Safecast/Solarcast/air-module/Bottom.png

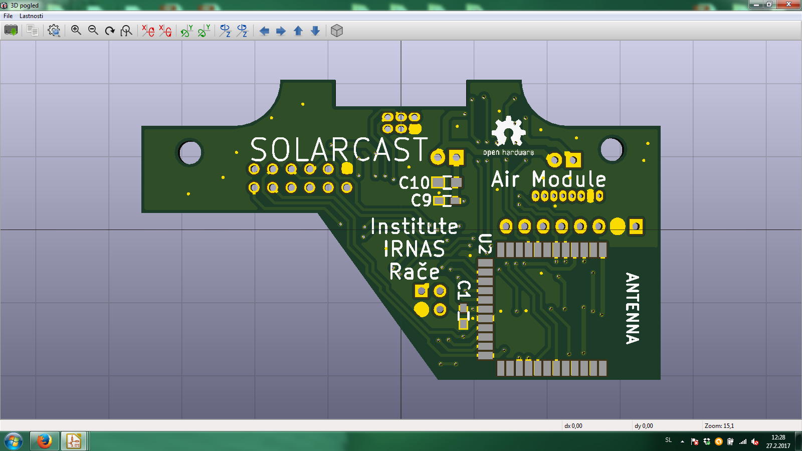
air-module/Bottom.png
