Safecast/Solarcast/air-module/Top.png

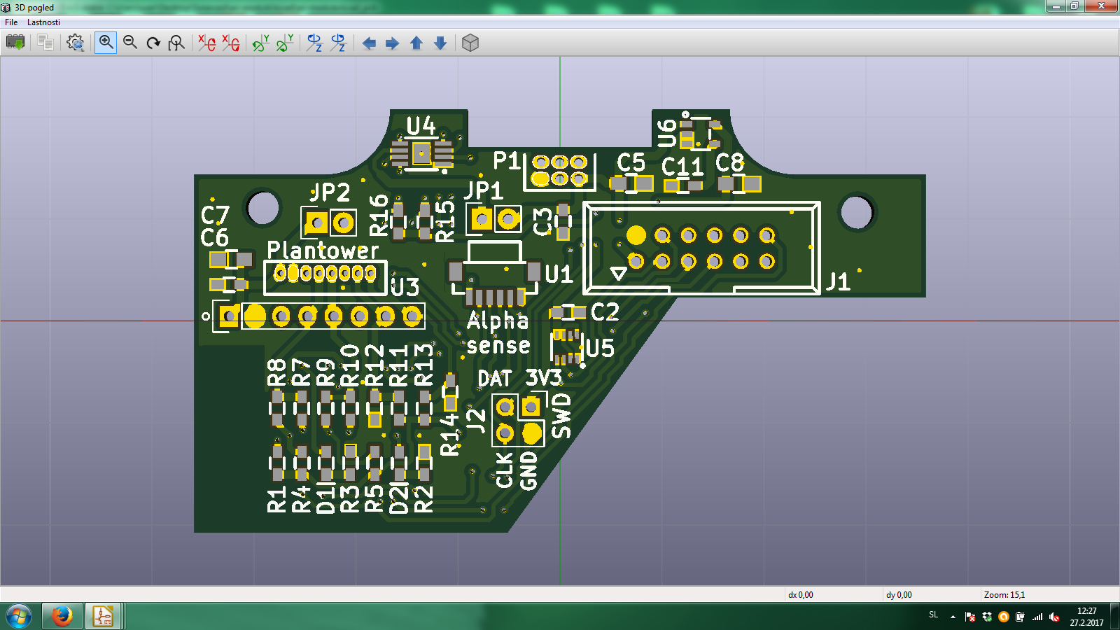
air-module/Top.png
