Safecast/Solarcast/communications-module/bottom.png

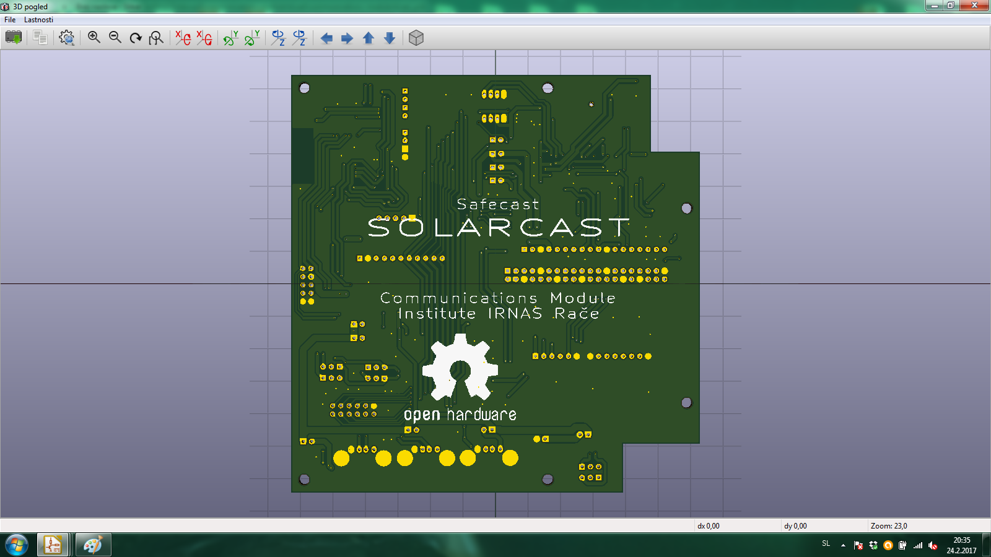
communications-module/bottom.png
