Safecast/Solarcast/communications-module/top.png

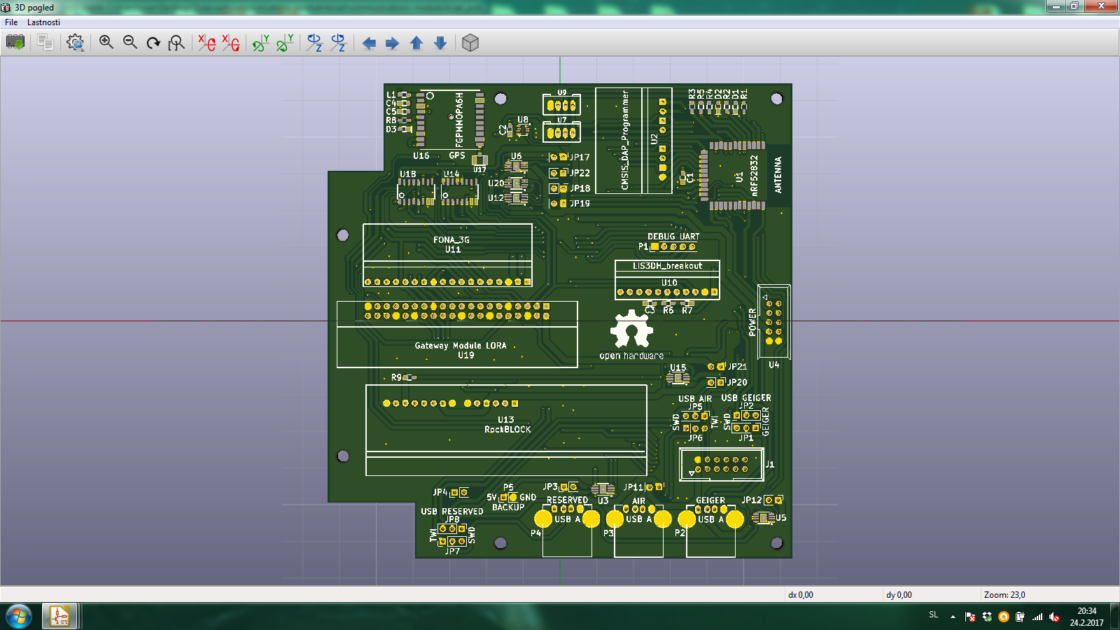
communications-module/top.png
