Safecast/Solarcast/gateway-module/bottom.png

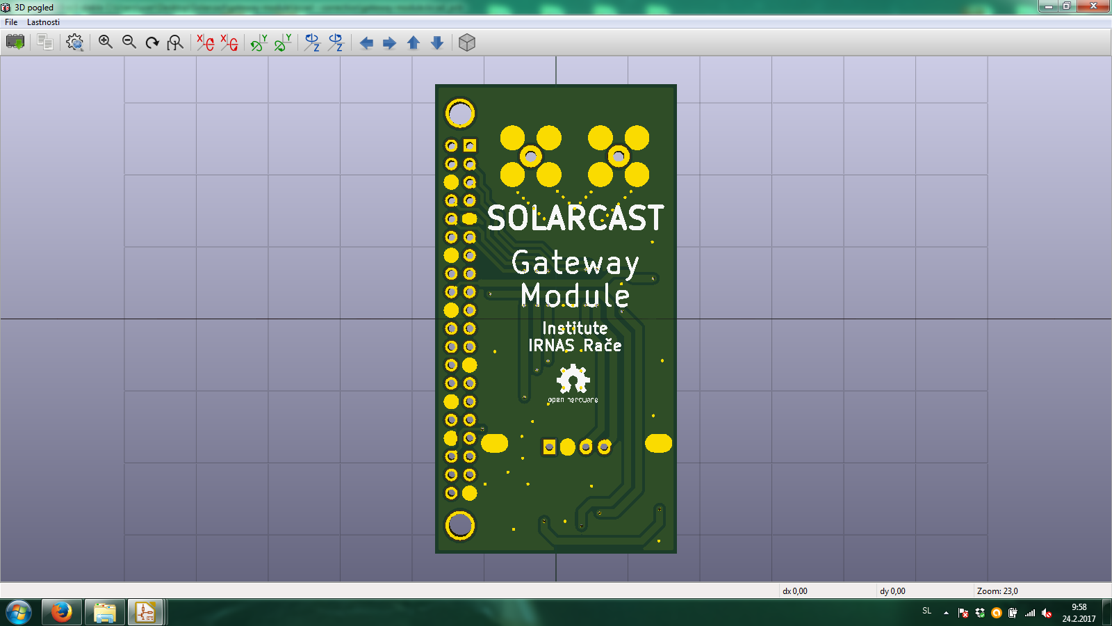
gateway-module/bottom.png
