Safecast/Solarcast/gateway-module/top.png

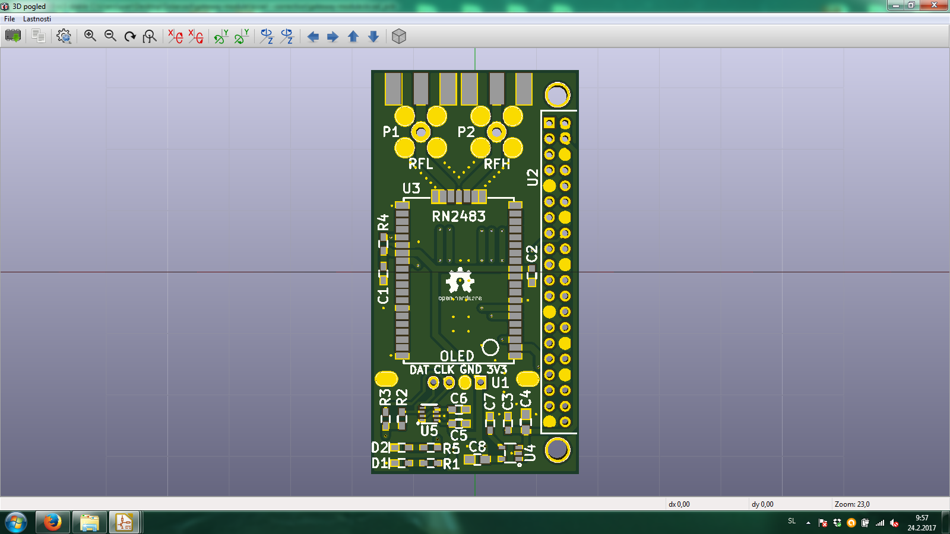
gateway-module/top.png
