Safecast/Solarcast/geiger-module/bottom.png

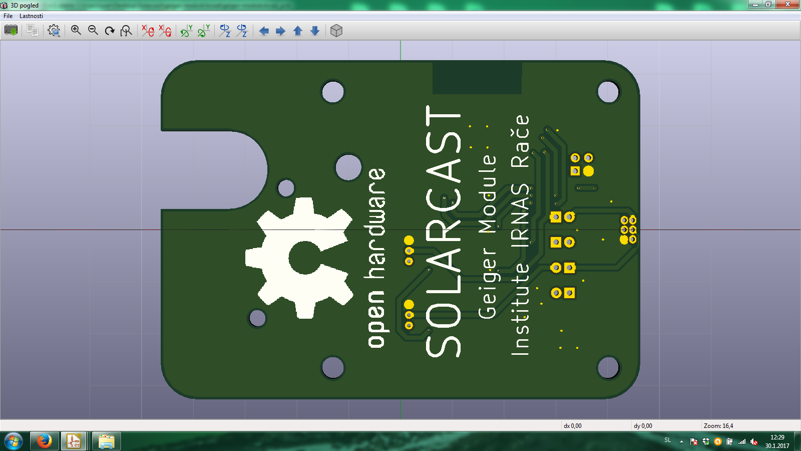
geiger-module/bottom.png
