Safecast/Solarcast/geiger-module/top.png

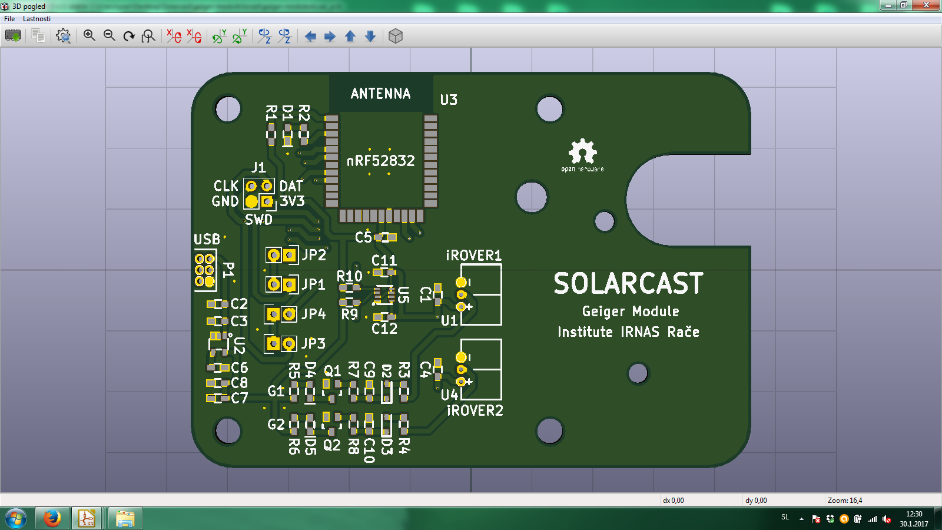
geiger-module/top.png
