Safecast/Solarcast/plantower-adapter/bottom.png

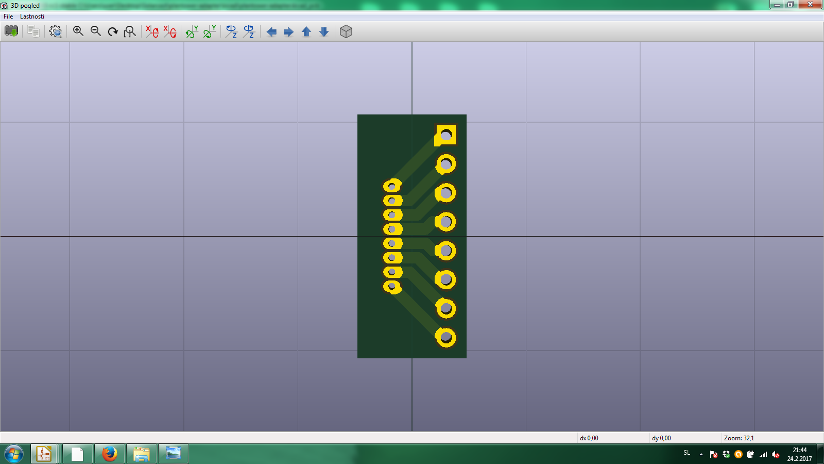
plantower-adapter/bottom.png
