Safecast/Solarcast/air-module/gerbers/air-module-B_Mask.pdf

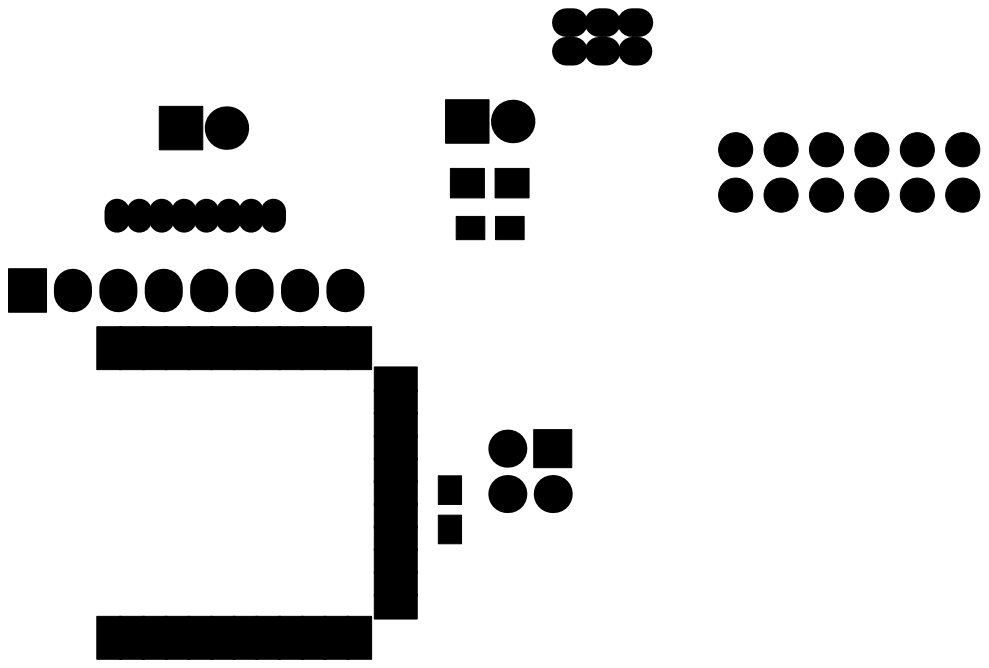
[picture p123: page 1]
