Safecast/Solarcast/air-module/gerbers/air-module-B_SilkS.pdf

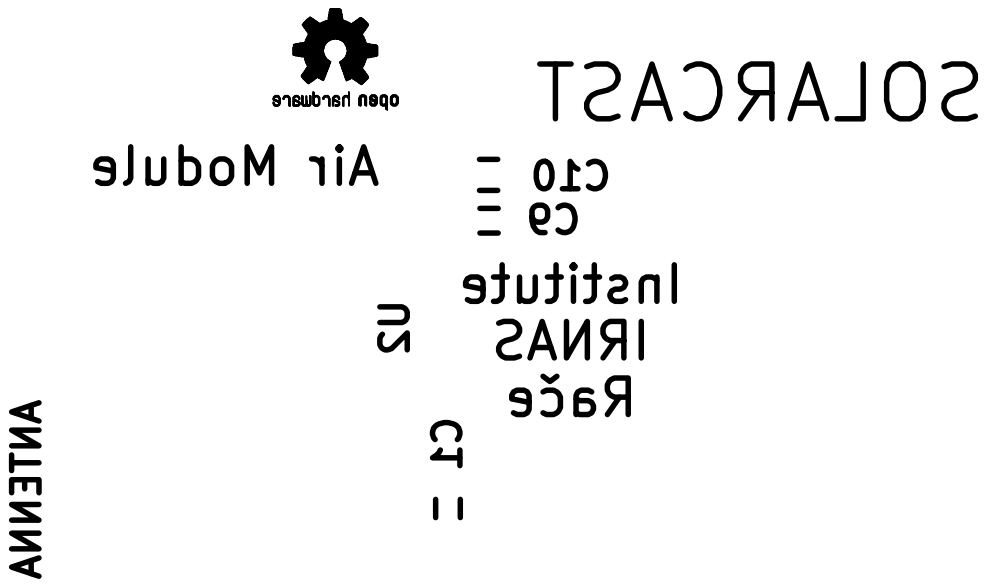
[picture p124: page 1]
