Safecast/Solarcast/air-module/gerbers/air-module-Edge_Cuts.pdf

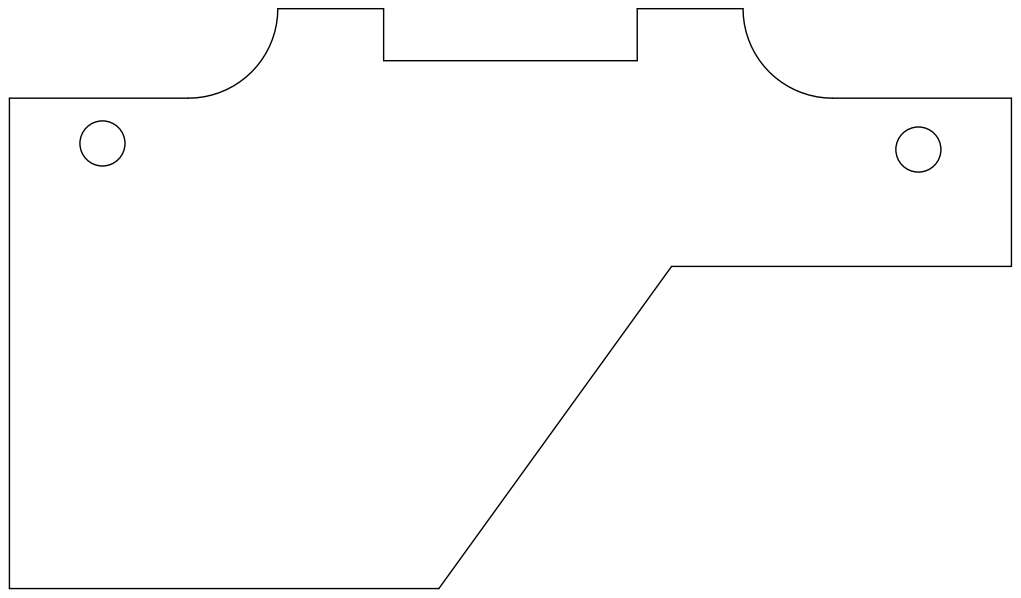
[picture p125: page 1]
