Safecast/Solarcast/air-module/gerbers/air-module-F_Cu.pdf

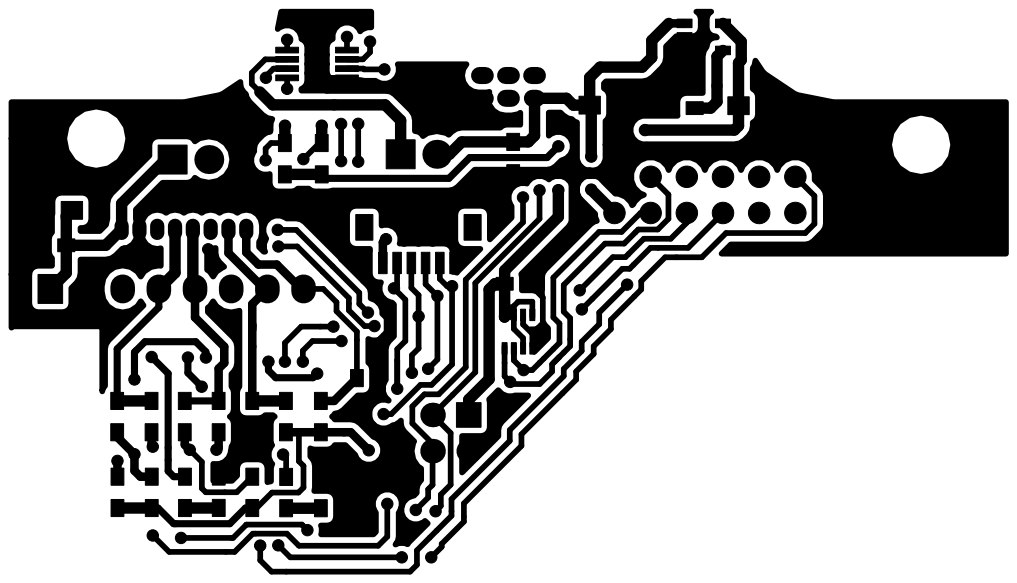
[picture p126: page 1]
