Safecast/Solarcast/air-module/gerbers/air-module-F_Mask.pdf

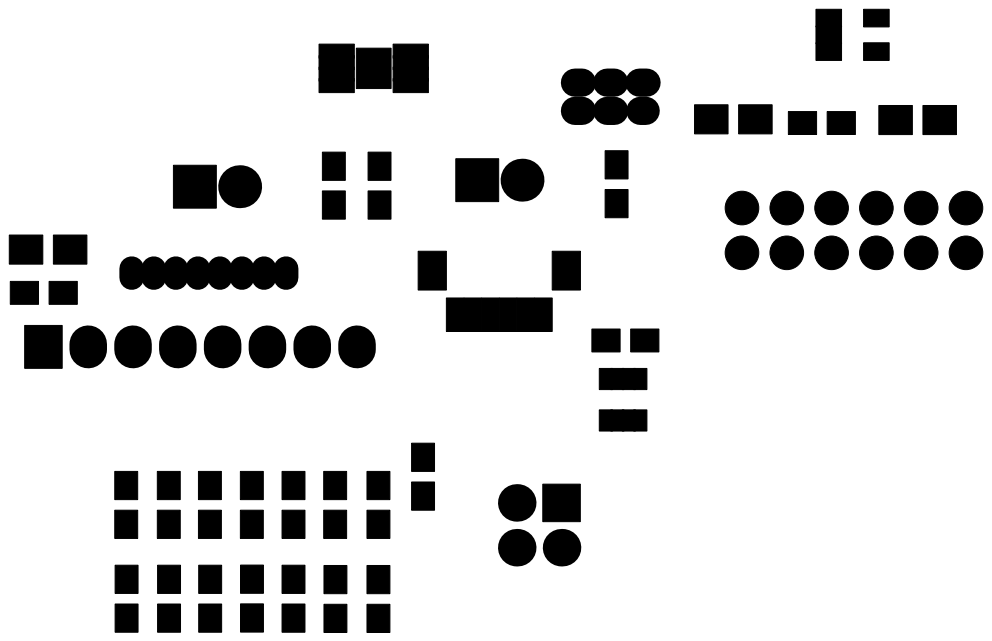
[picture p127: page 1]
