Safecast/Solarcast/air-module/gerbers/air-module-F_SilkS.pdf

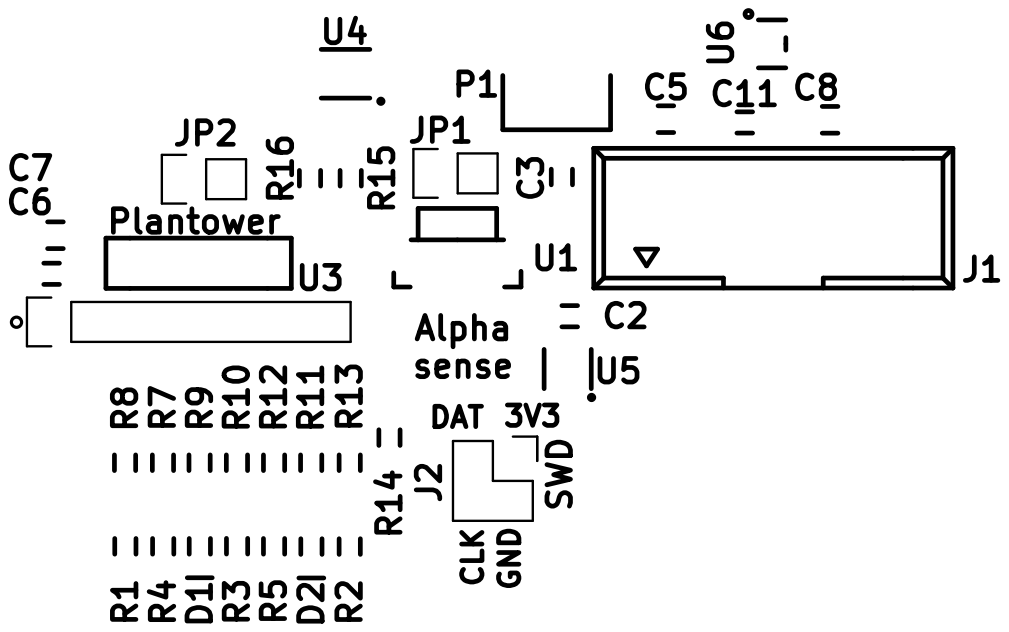
[picture p128: page 1]
