Safecast/Solarcast/plantower-adapter/gerbers/plantower-adapter-B_Cu.pdf

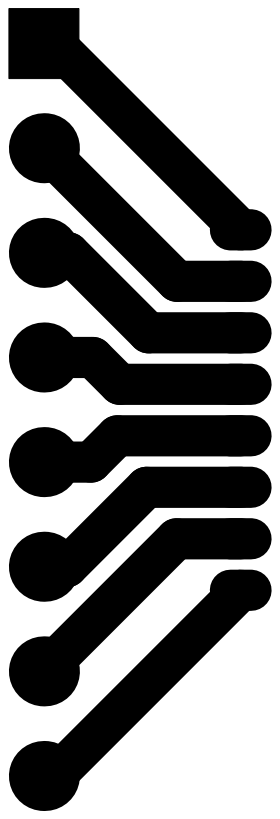
[picture p129: page 1]
