Safecast/Solarcast/communications-module/gerbers/communications-module-B_Cu.pdf

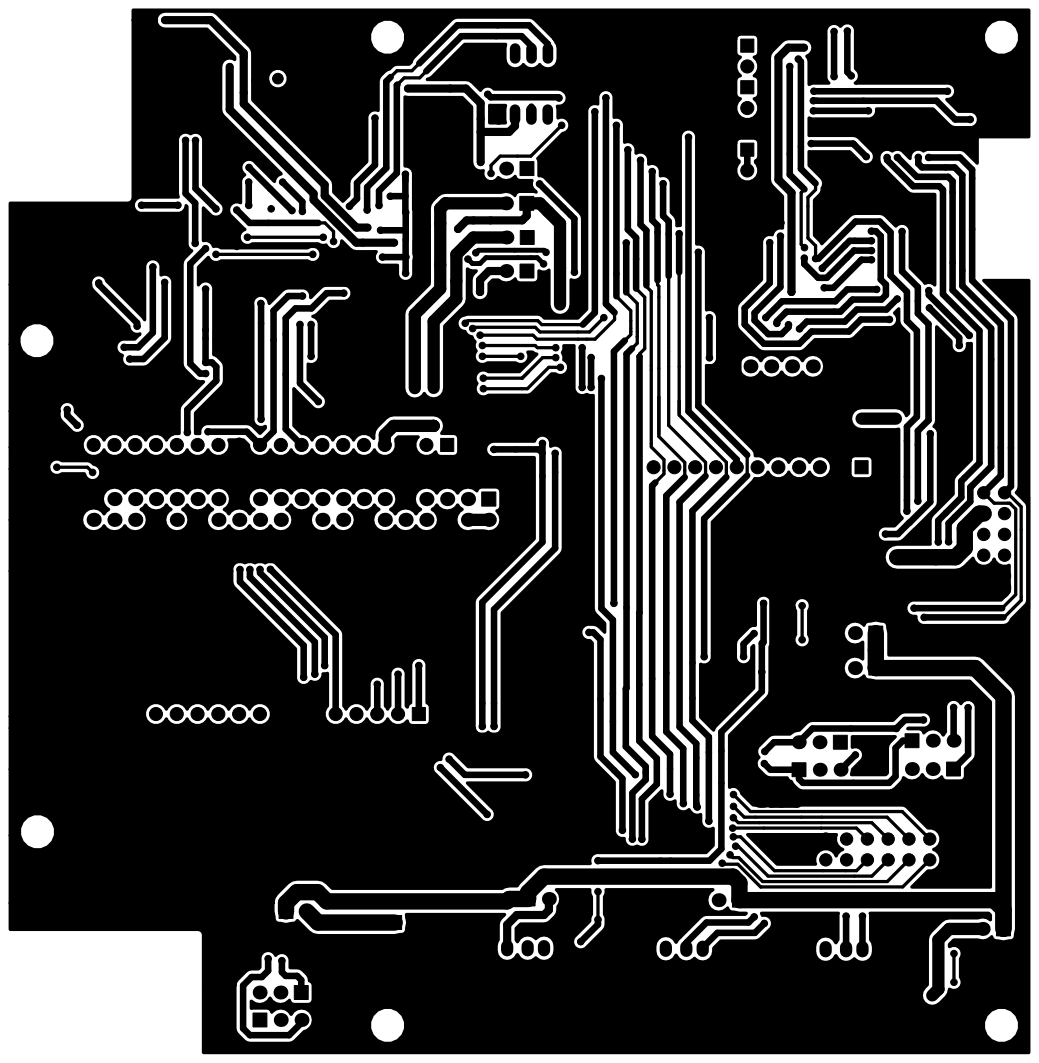
[picture p130: page 1]
