Safecast/Solarcast/communications-module/gerbers/communications-module-B_Mask.pdf

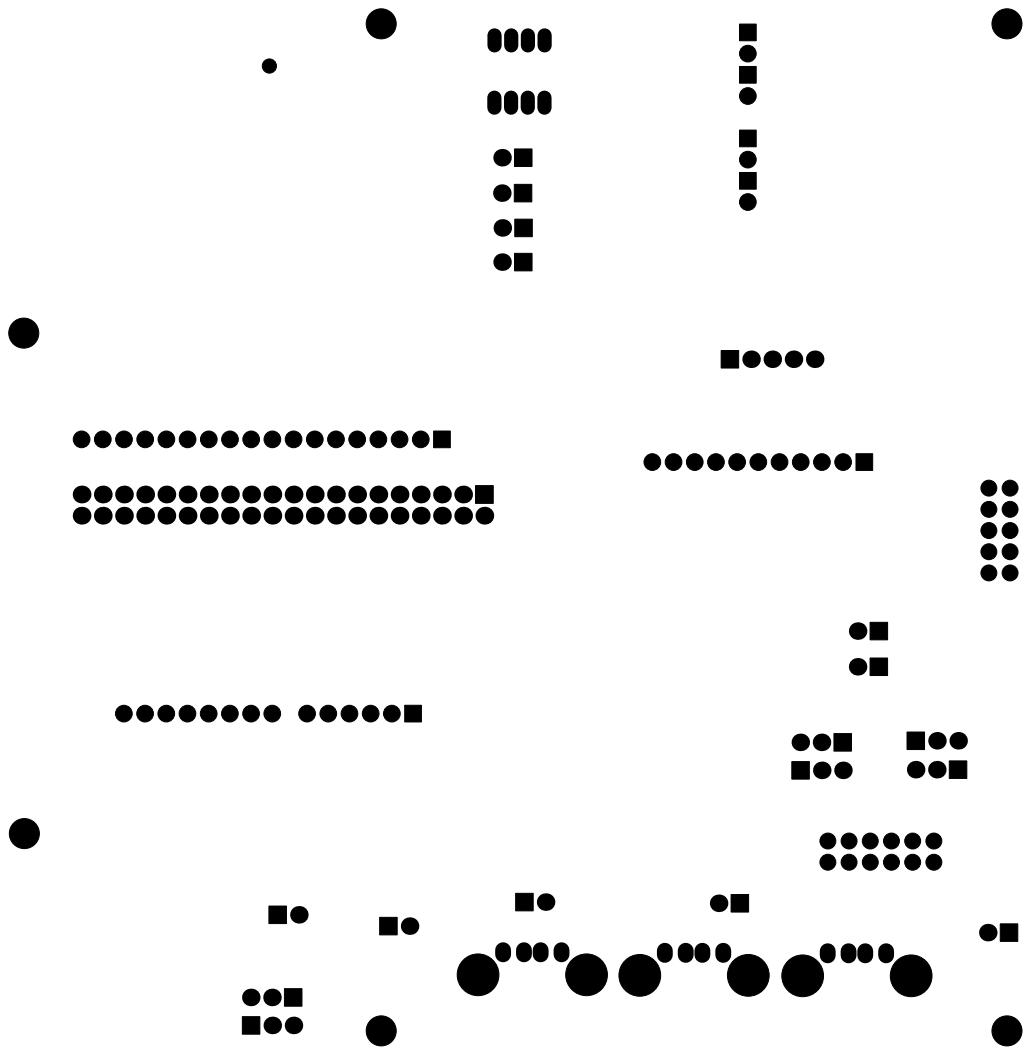
[picture p131: page 1]
