Safecast/Solarcast/communications-module/gerbers/communications-module-B_SilkS.pdf

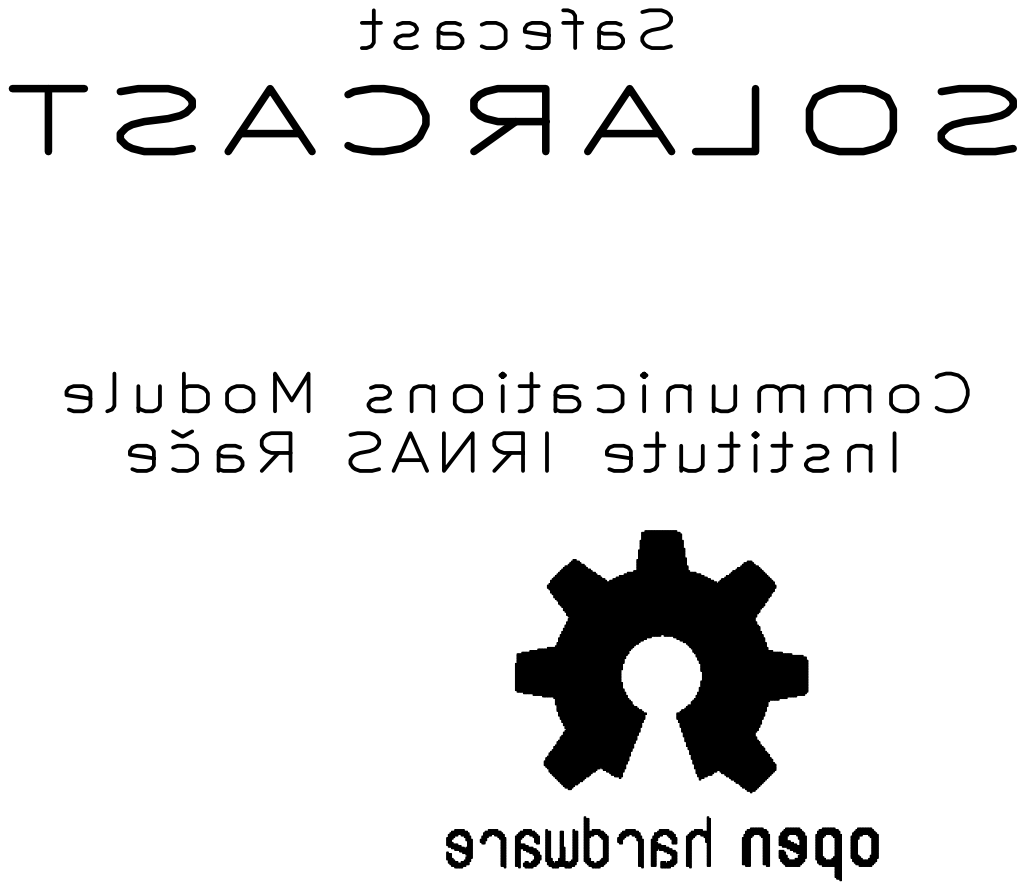
[picture p132: page 1]
