Safecast/Solarcast/communications-module/gerbers/communications-module-F_Cu.pdf

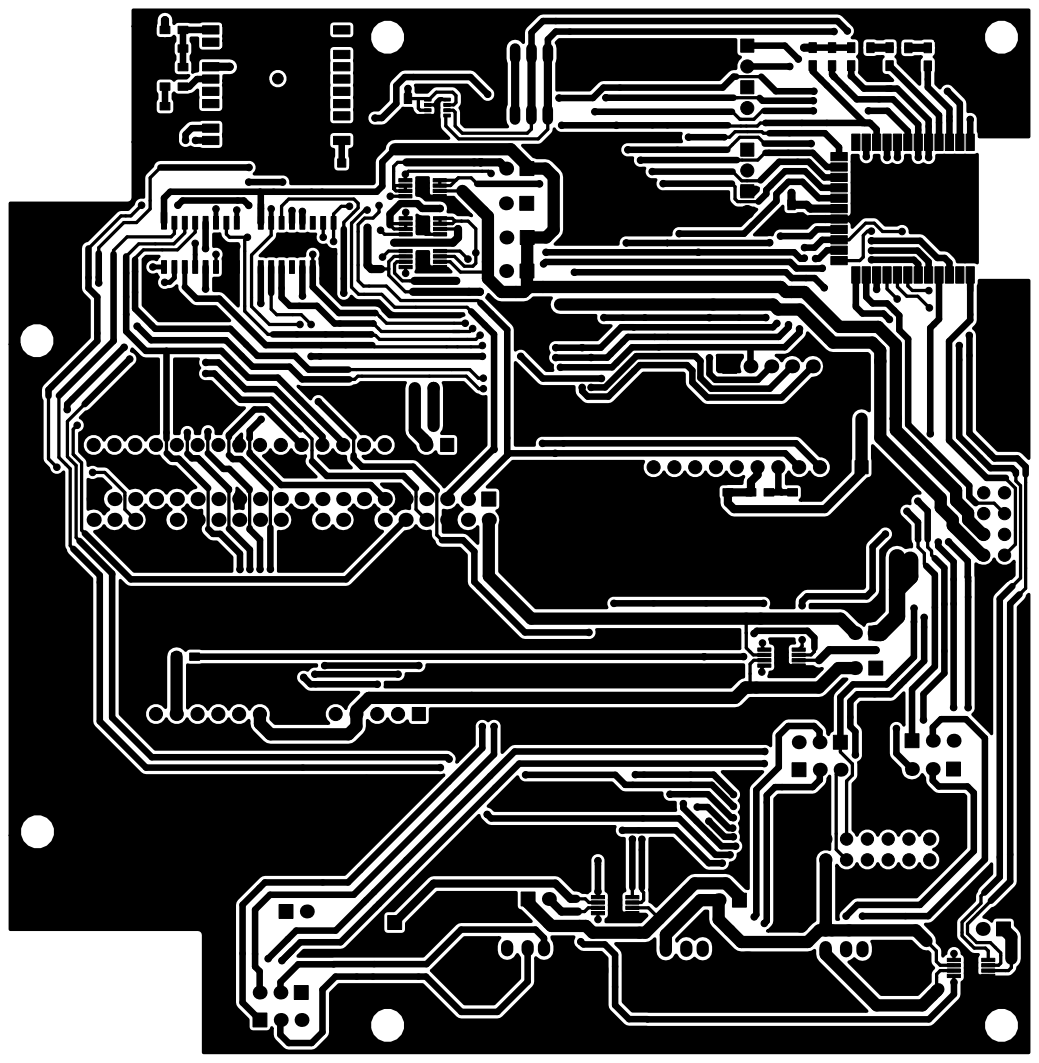
[picture p133: page 1]
