Safecast/Solarcast/communications-module/gerbers/communications-module-F_Mask.pdf

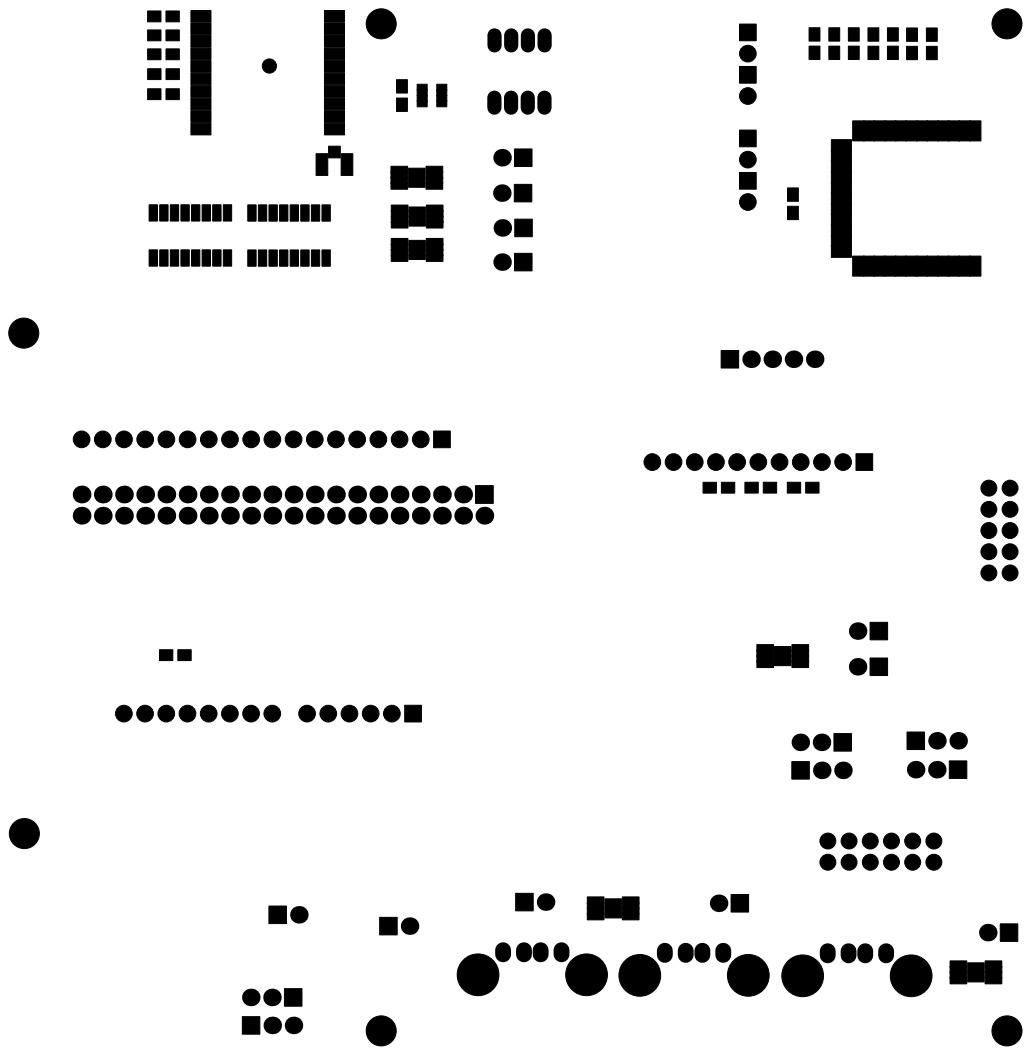
[picture p134: page 1]
