Safecast/Solarcast/communications-module/gerbers/communications-module-F_SilkS.pdf

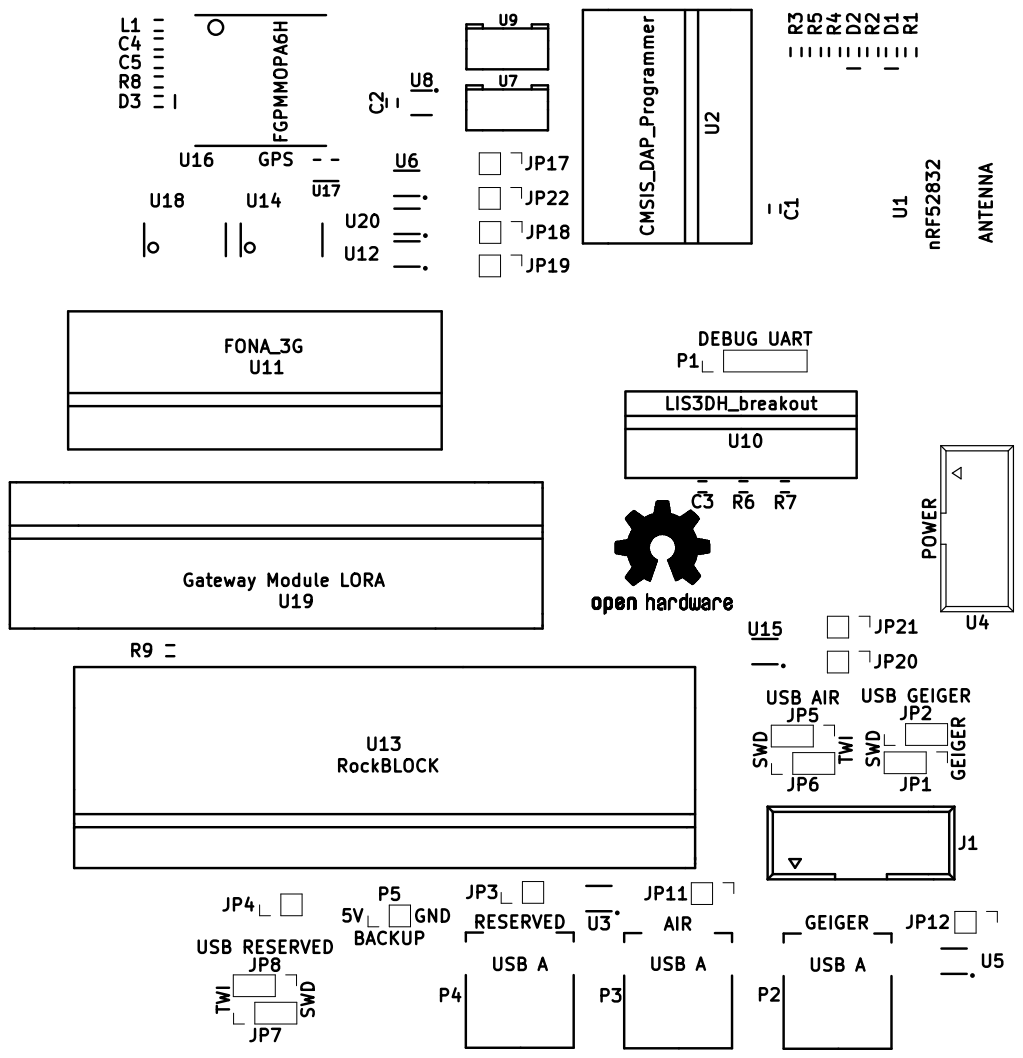
[picture p135: page 1]
