Safecast/Solarcast/gateway-module/gerbers/gateway-module-B_Cu.pdf

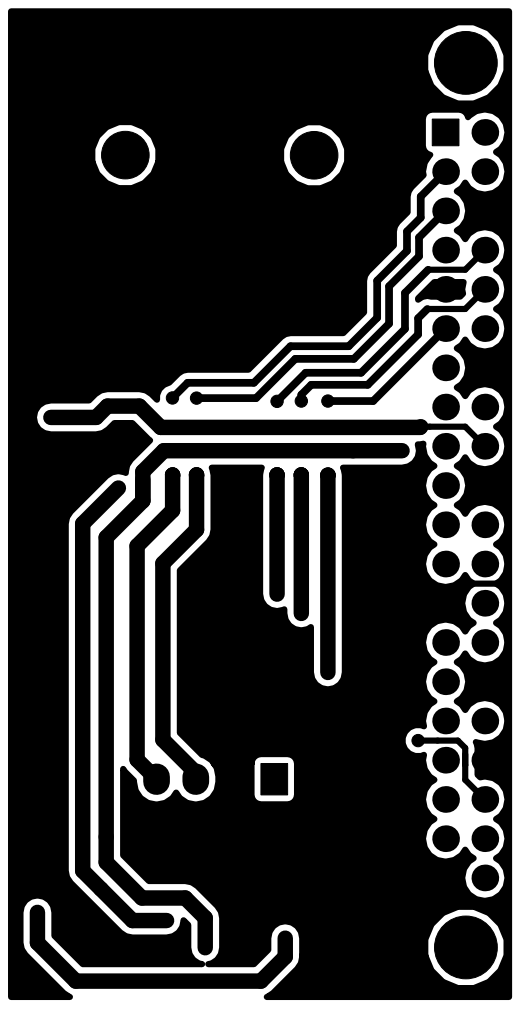
[picture p136: page 1]
