Safecast/Solarcast/gateway-module/gerbers/gateway-module-B_Mask.pdf

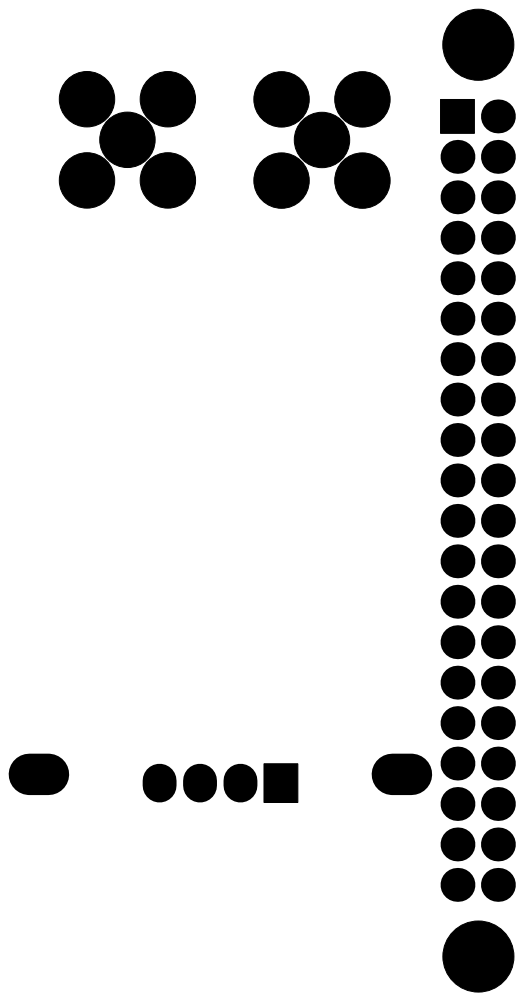
[picture p137: page 1]
