Safecast/Solarcast/gateway-module/gerbers/gateway-module-B_SilkS.pdf

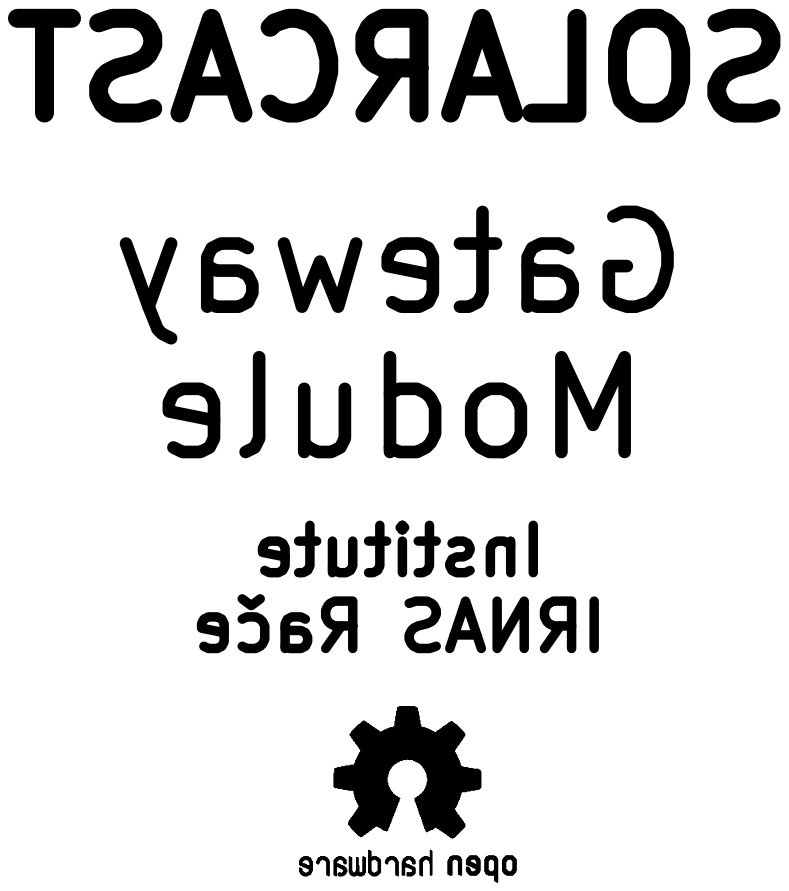
[picture p138: page 1]
