Safecast/Solarcast/gateway-module/gerbers/gateway-module-F_Cu.pdf

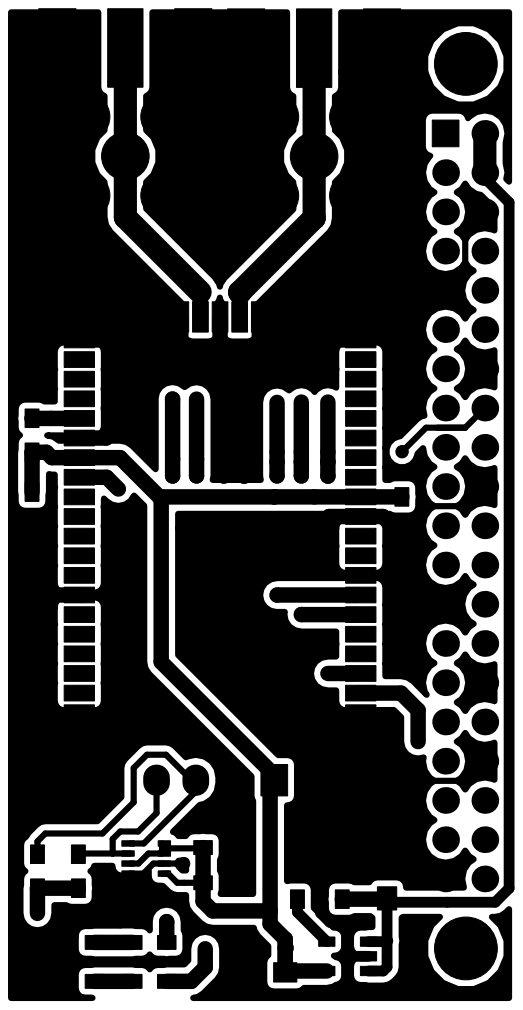
[picture p139: page 1]
