Safecast/Solarcast/gateway-module/gerbers/gateway-module-F_Mask.pdf

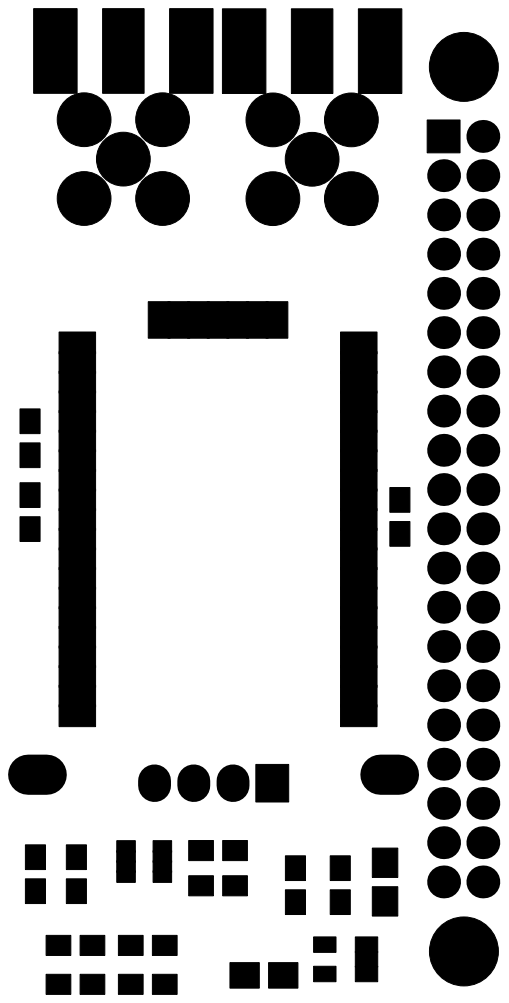
[picture p140: page 1]
