Safecast/Solarcast/gateway-module/gerbers/gateway-module-F_SilkS.pdf

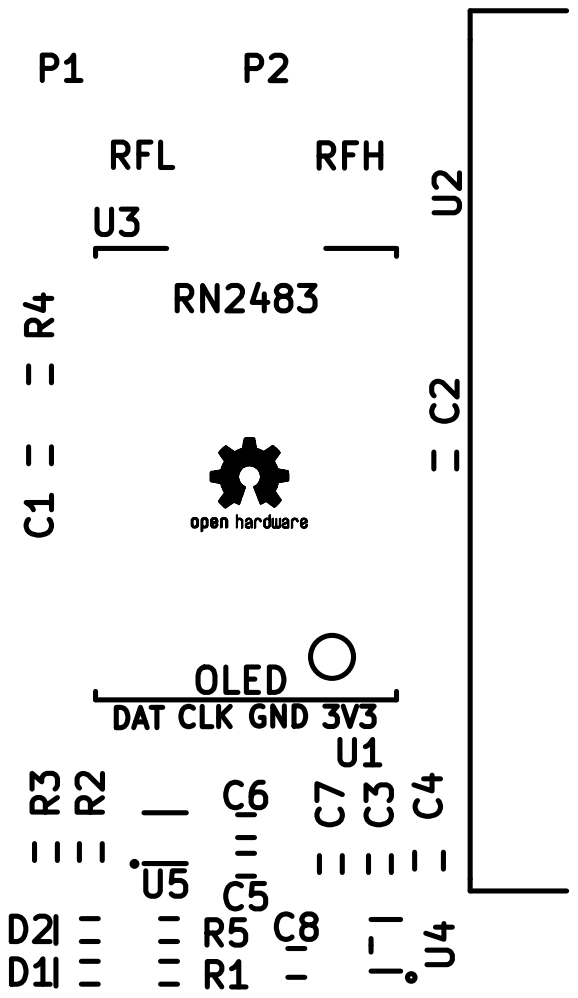
[picture p141: page 1]
