Safecast/Solarcast/gateway-module/kicad/gateway-module.pdf

File: gateway-module.sch Sheet: /
Id: 1/1 Title: Communications Module
