Safecast/Solarcast/geiger-module/gerbers/geiger-module-B_Cu.pdf

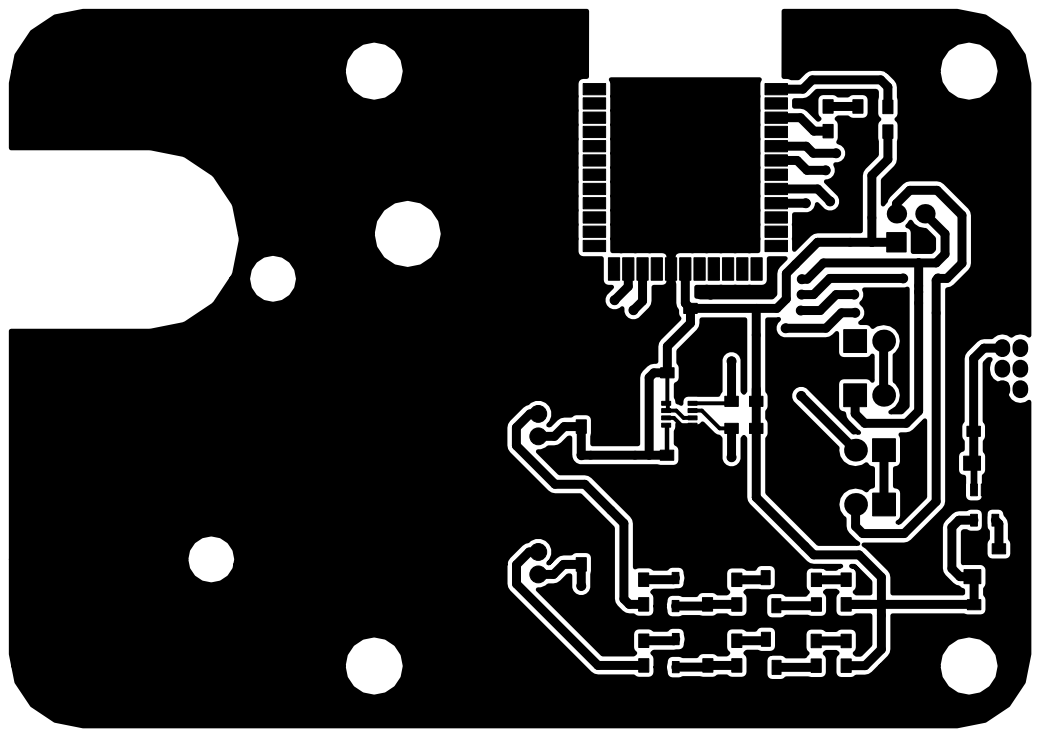
[picture p142: page 1]
