Safecast/Solarcast/geiger-module/gerbers/geiger-module-B_Mask.pdf

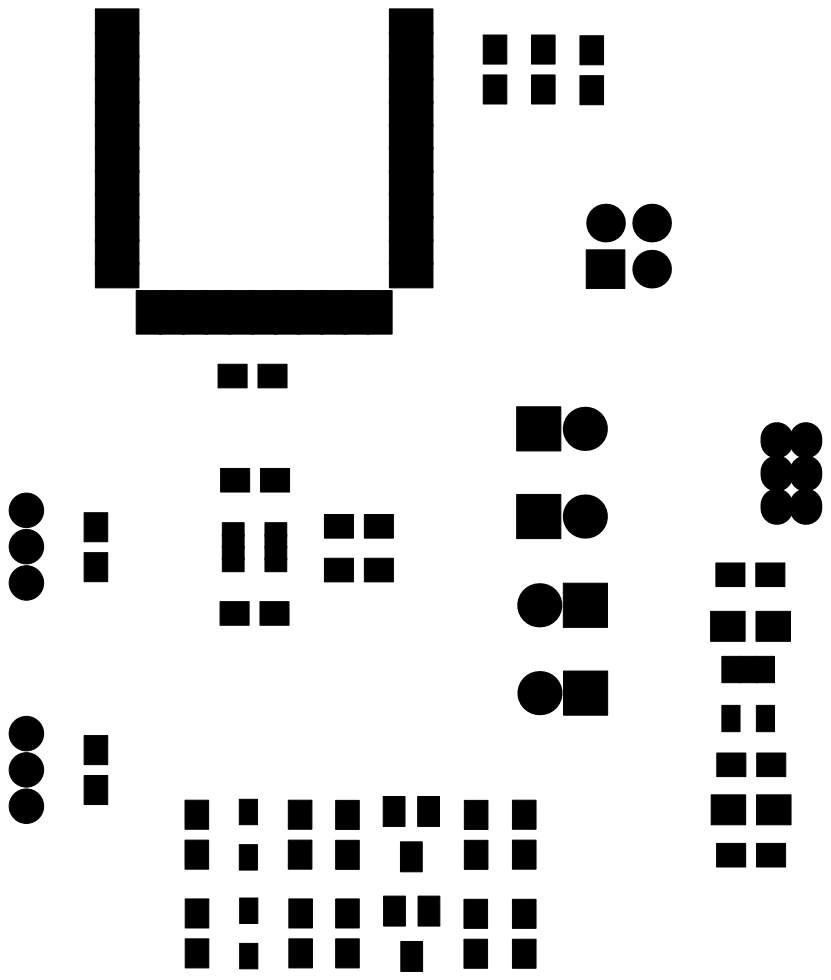
[picture p143: page 1]
