Safecast/Solarcast/geiger-module/gerbers/geiger-module-B_SilkS.pdf

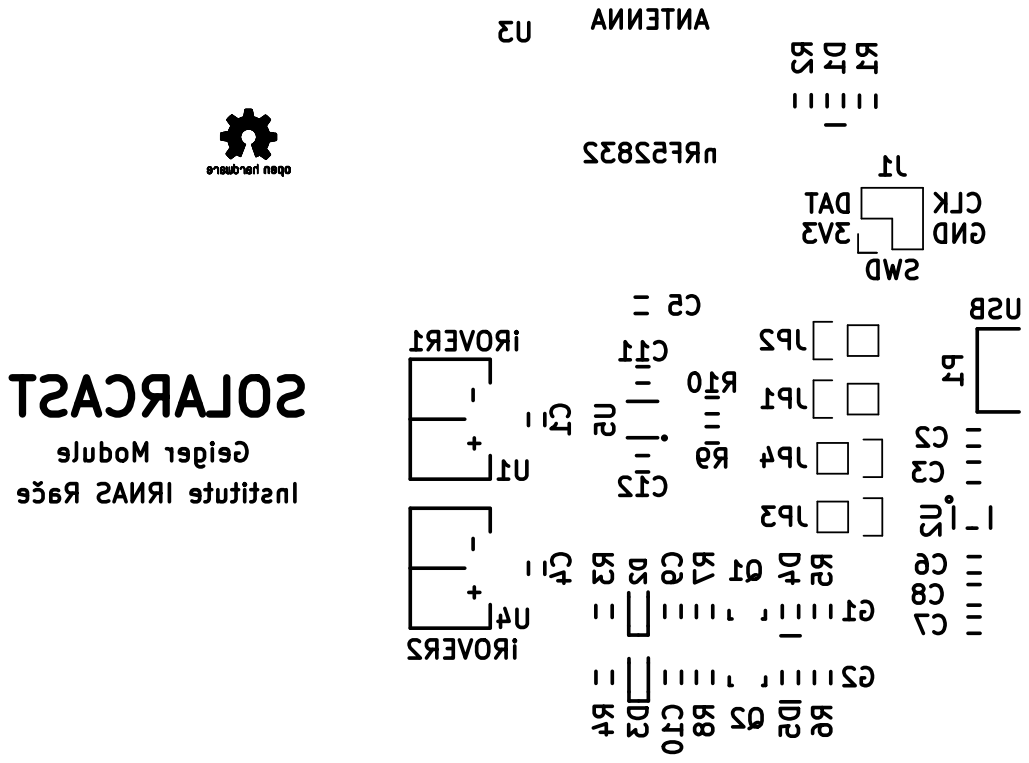
[picture p144: page 1]

Institute IRNAS Rae Geiger Module
