Safecast/Solarcast/geiger-module/gerbers/geiger-module-Edge_Cuts.pdf

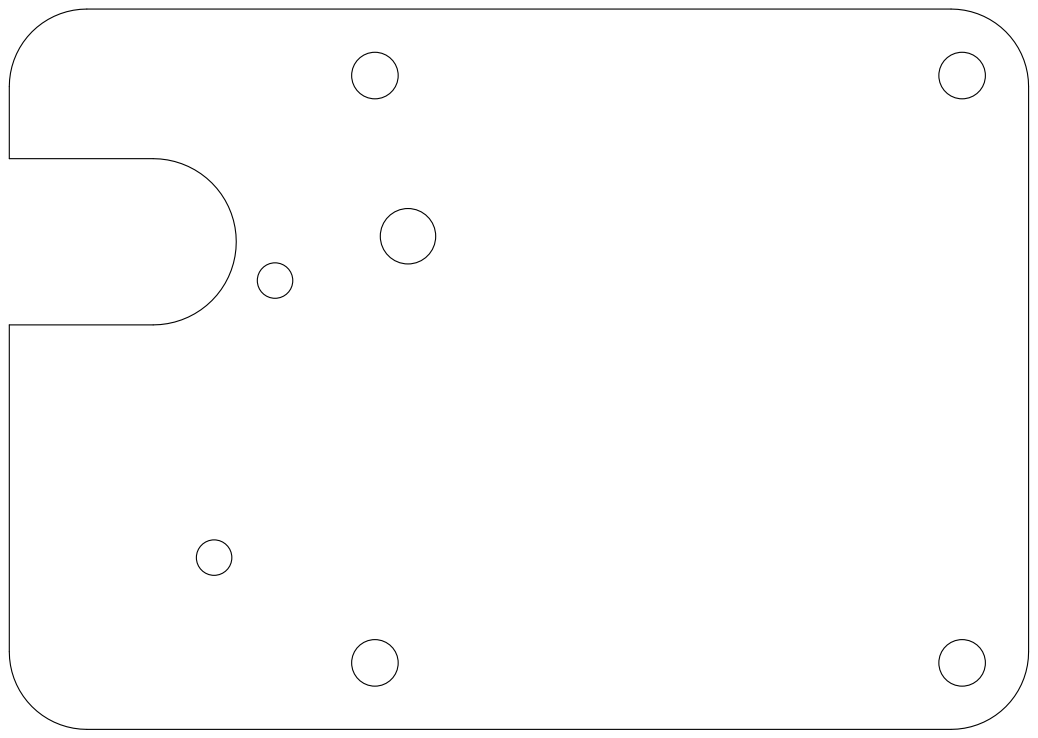
[picture p145: page 1]
