Safecast/Solarcast/geiger-module/gerbers/geiger-module-F_Cu.pdf

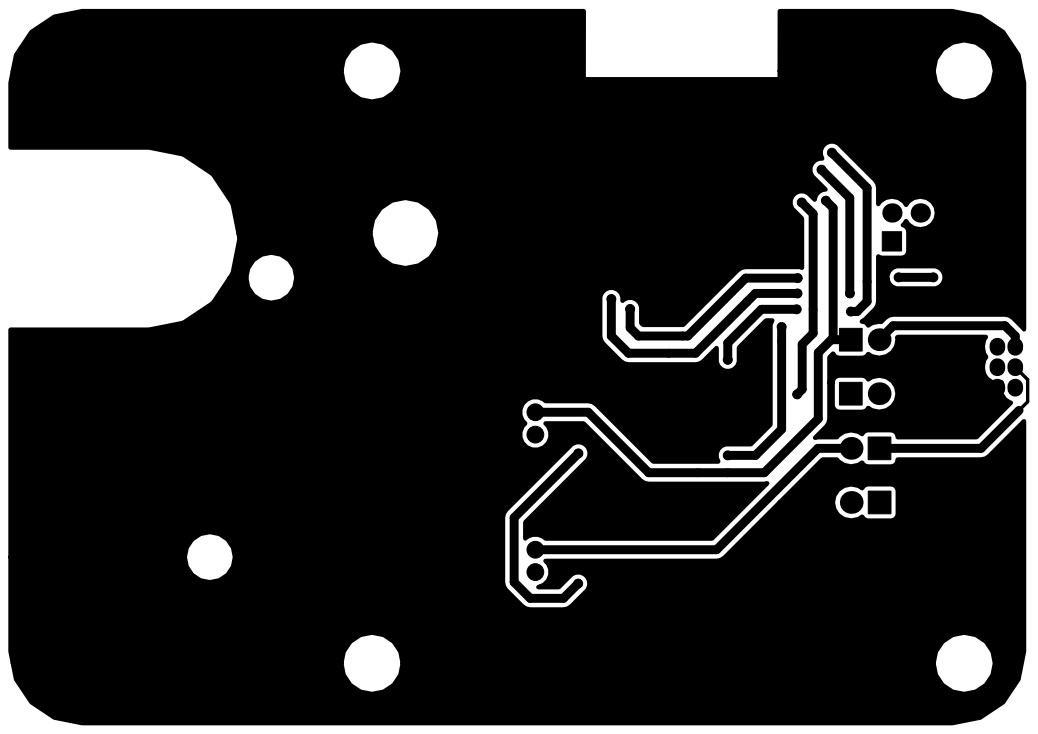
[picture p146: page 1]
