Safecast/Solarcast/geiger-module/gerbers/geiger-module-F_Mask.pdf

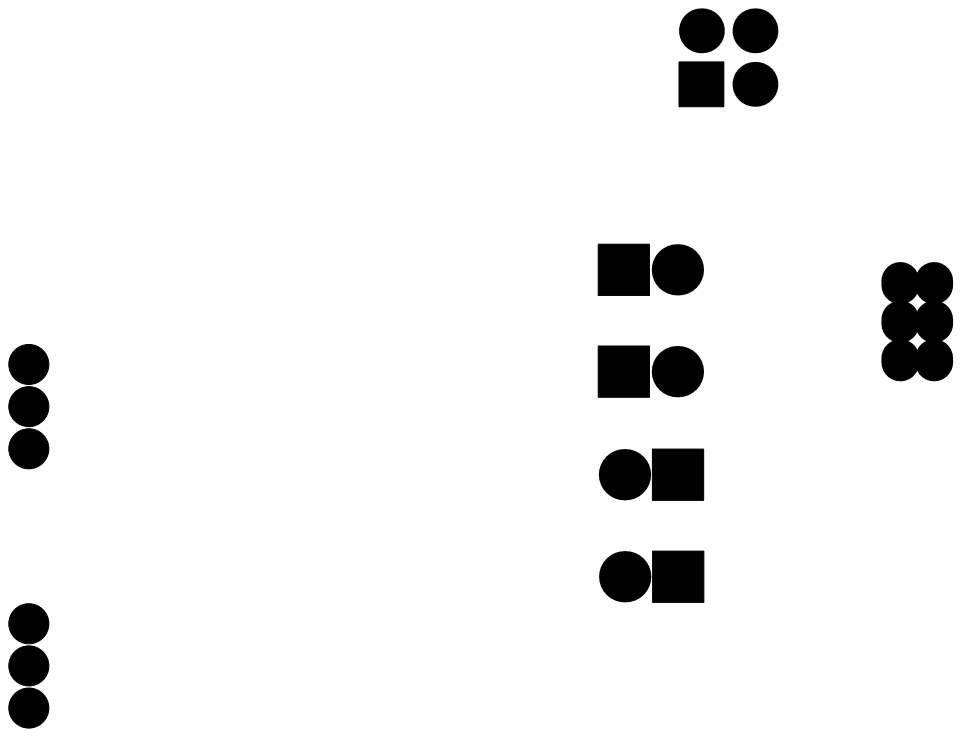
[picture p147: page 1]
