Safecast/Solarcast/geiger-module/gerbers/geiger-module-F_SilkS.pdf

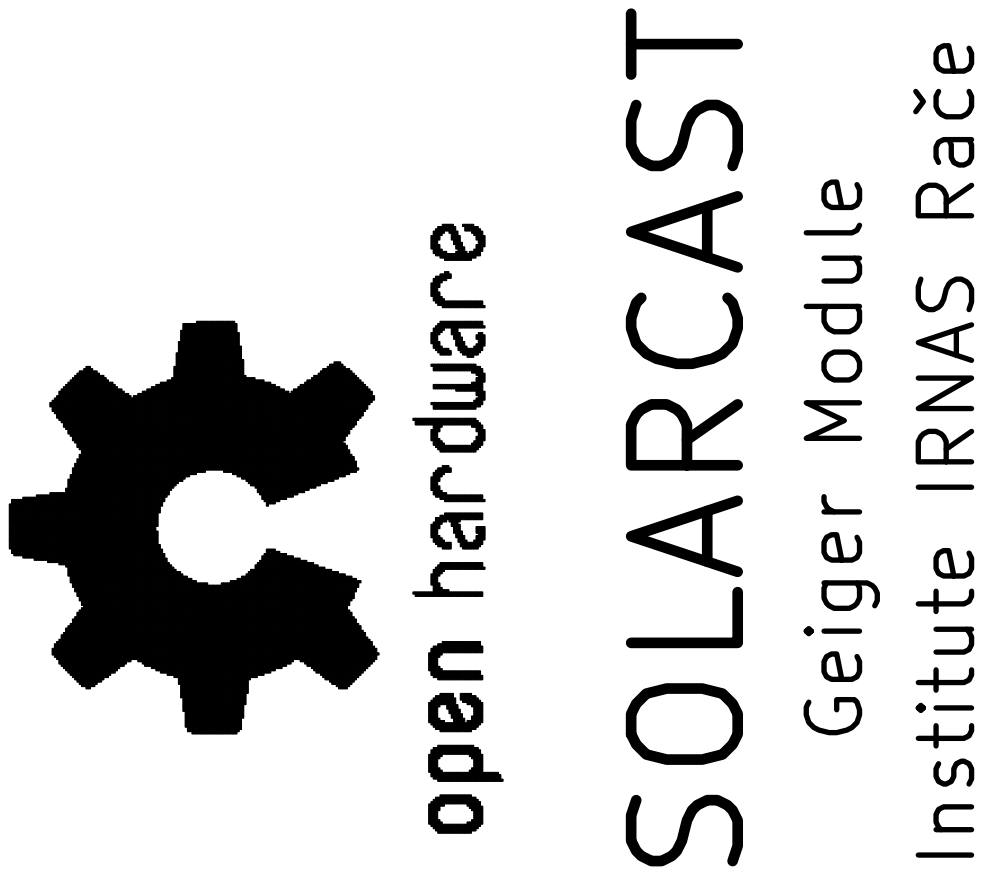
[picture p148: page 1]

Institute IRNAS Rae Geiger Module SOLARCAST
