Safecast/Solarcast/geiger-module/kicad/geiger-module.pdf

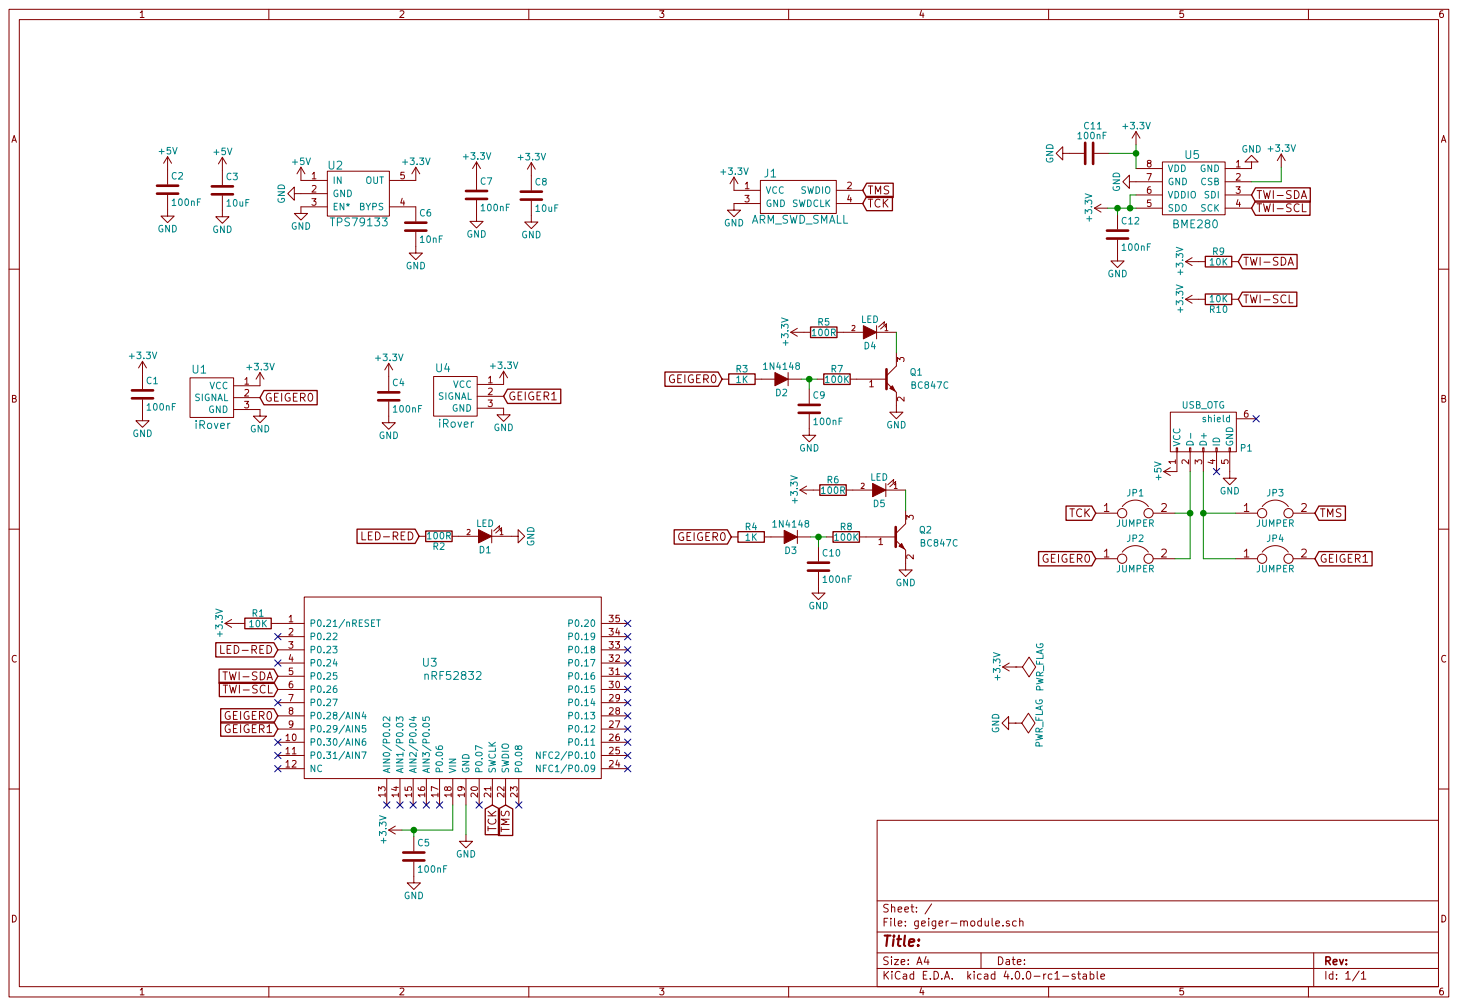
[picture p149: page 1]
