Safecast/Solarcast/air-module/kicad/gerbers/air-module-B_Cu.pdf

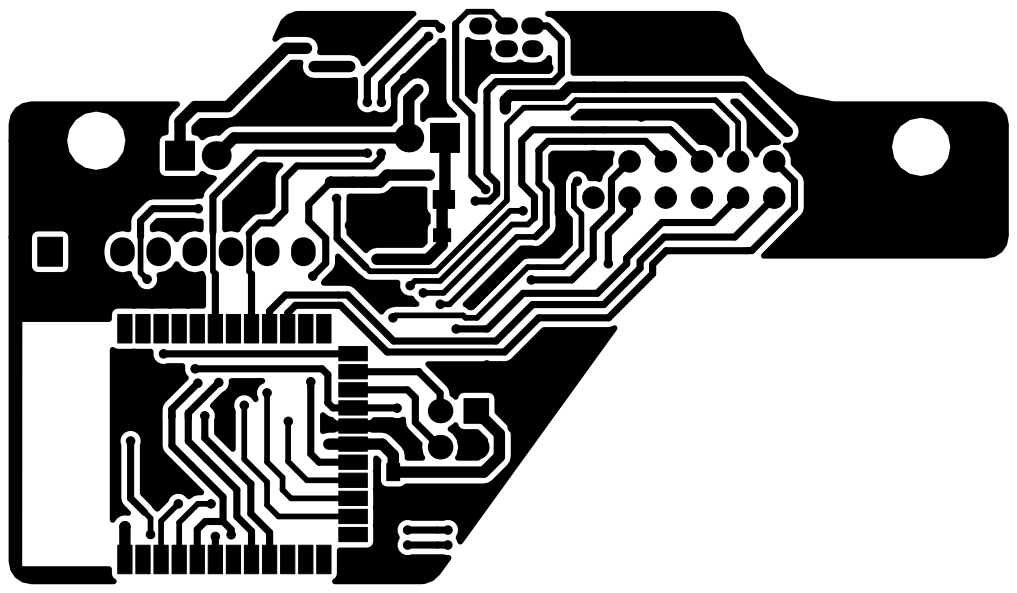
[picture p150: page 1]
