Safecast/Solarcast/air-module/kicad/gerbers/air-module-B_Mask.pdf

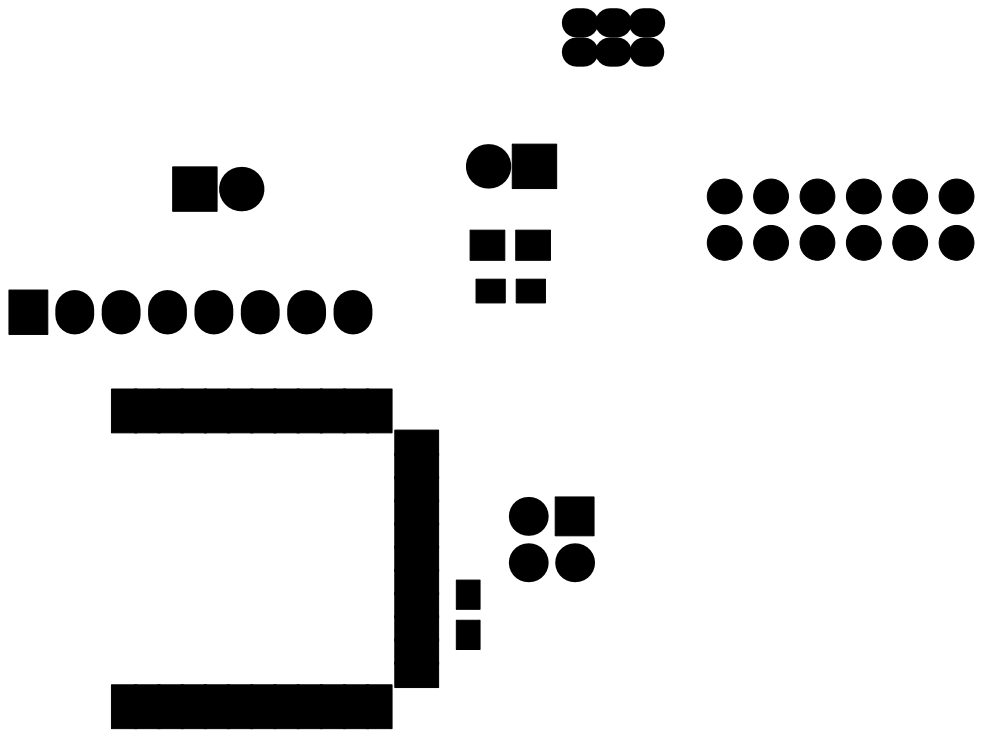
[picture p151: page 1]
