Safecast/Solarcast/air-module/kicad/gerbers/air-module-B_SilkS.pdf

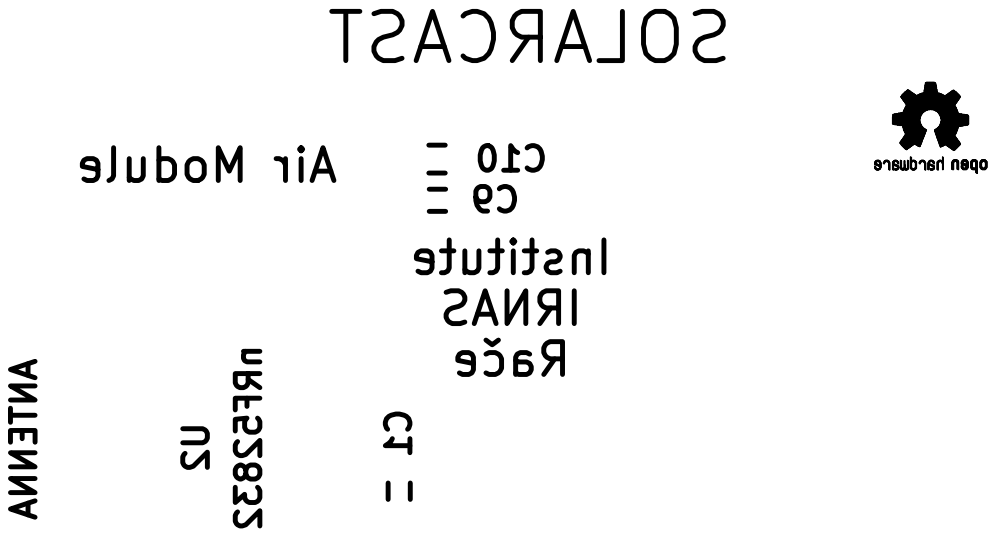
[picture p152: page 1]
