Safecast/Solarcast/air-module/kicad/gerbers/air-module-Edge_Cuts.pdf

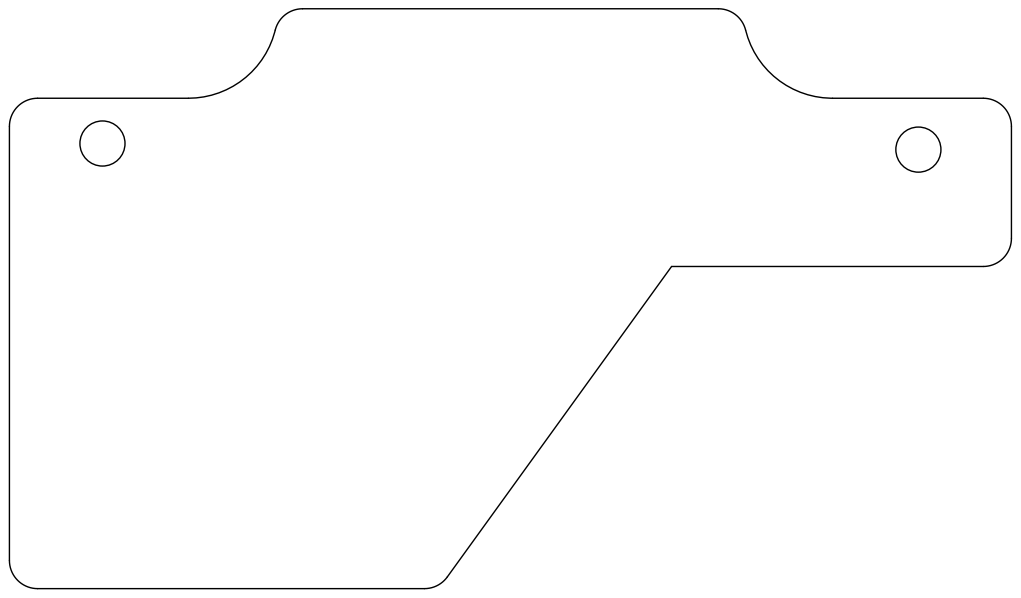
[picture p153: page 1]
