Safecast/Solarcast/air-module/kicad/gerbers/air-module-F_Cu.pdf

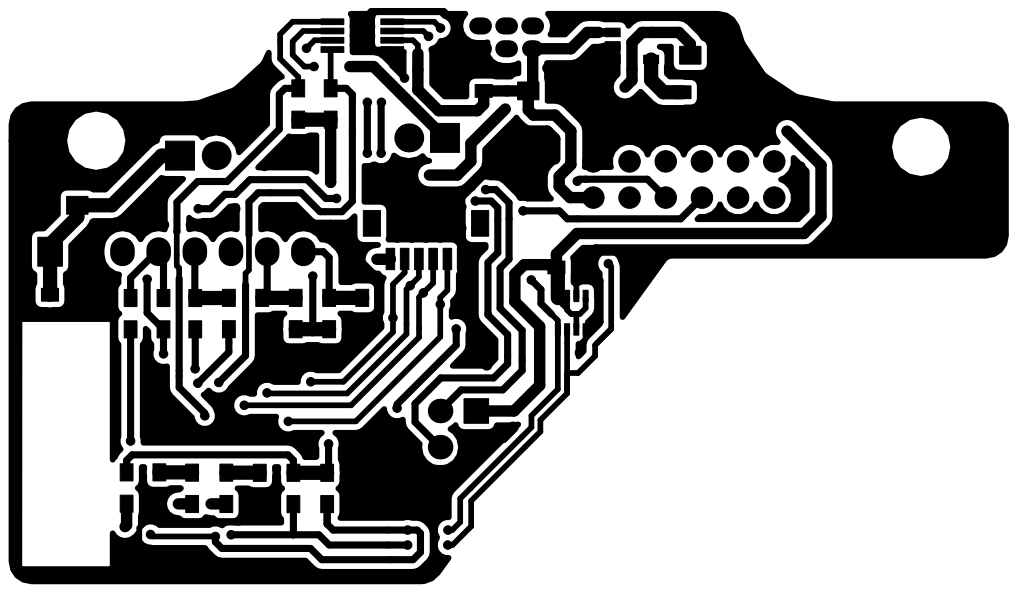
[picture p154: page 1]
