Safecast/Solarcast/air-module/kicad/gerbers/air-module-F_Mask.pdf

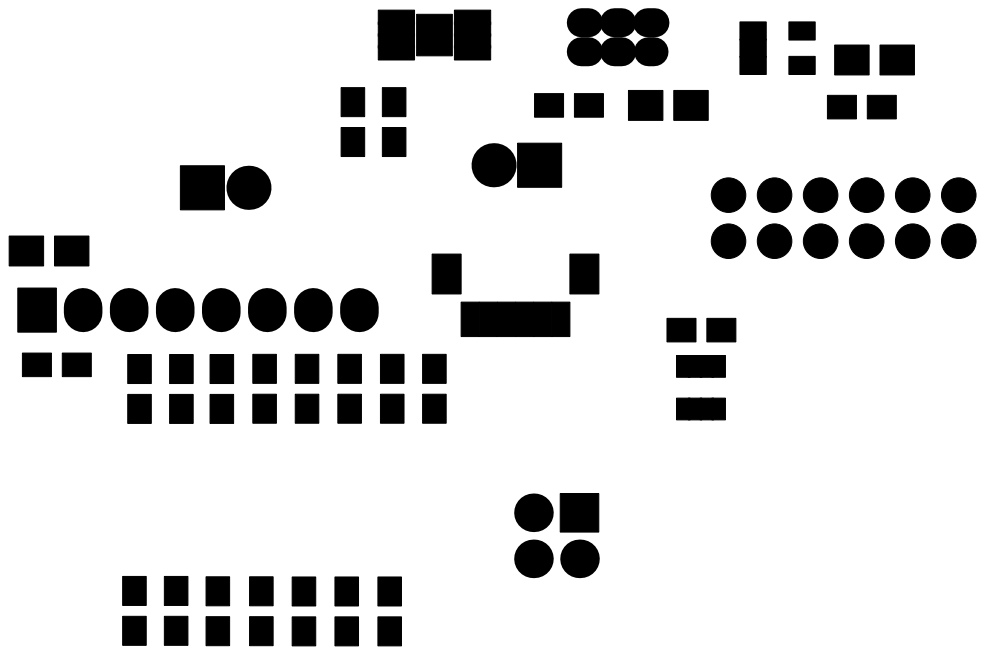
[picture p155: page 1]
