Safecast/Solarcast/air-module/kicad/gerbers/air-module-F_SilkS.pdf

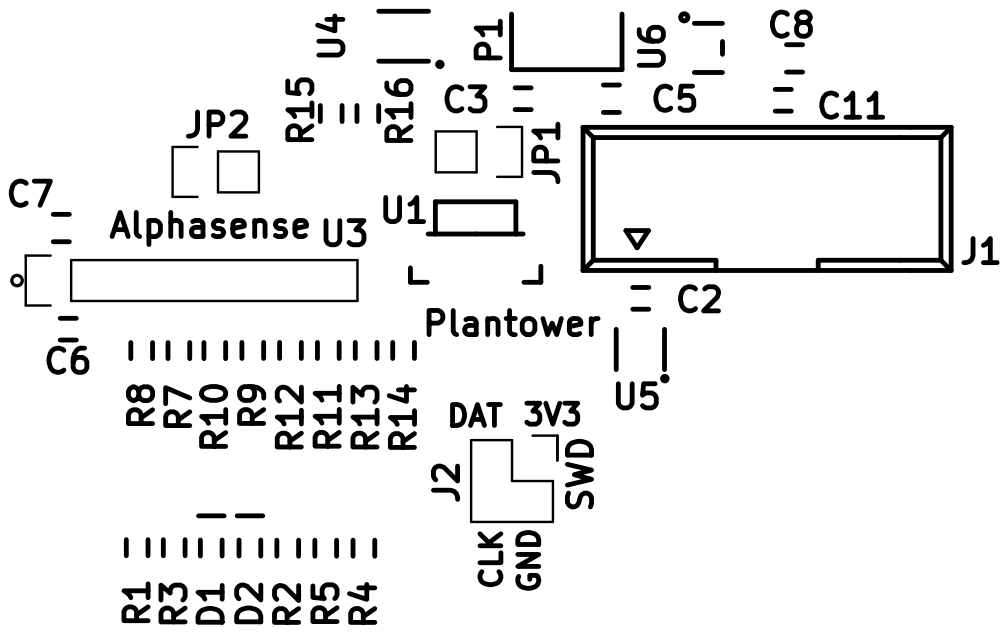
[picture p156: page 1]
