Safecast/Solarcast/gateway-module/kicad/gateway-module.sch

## KiCad design gateway-module/kicad/gateway-module.sch (2017-02-24)

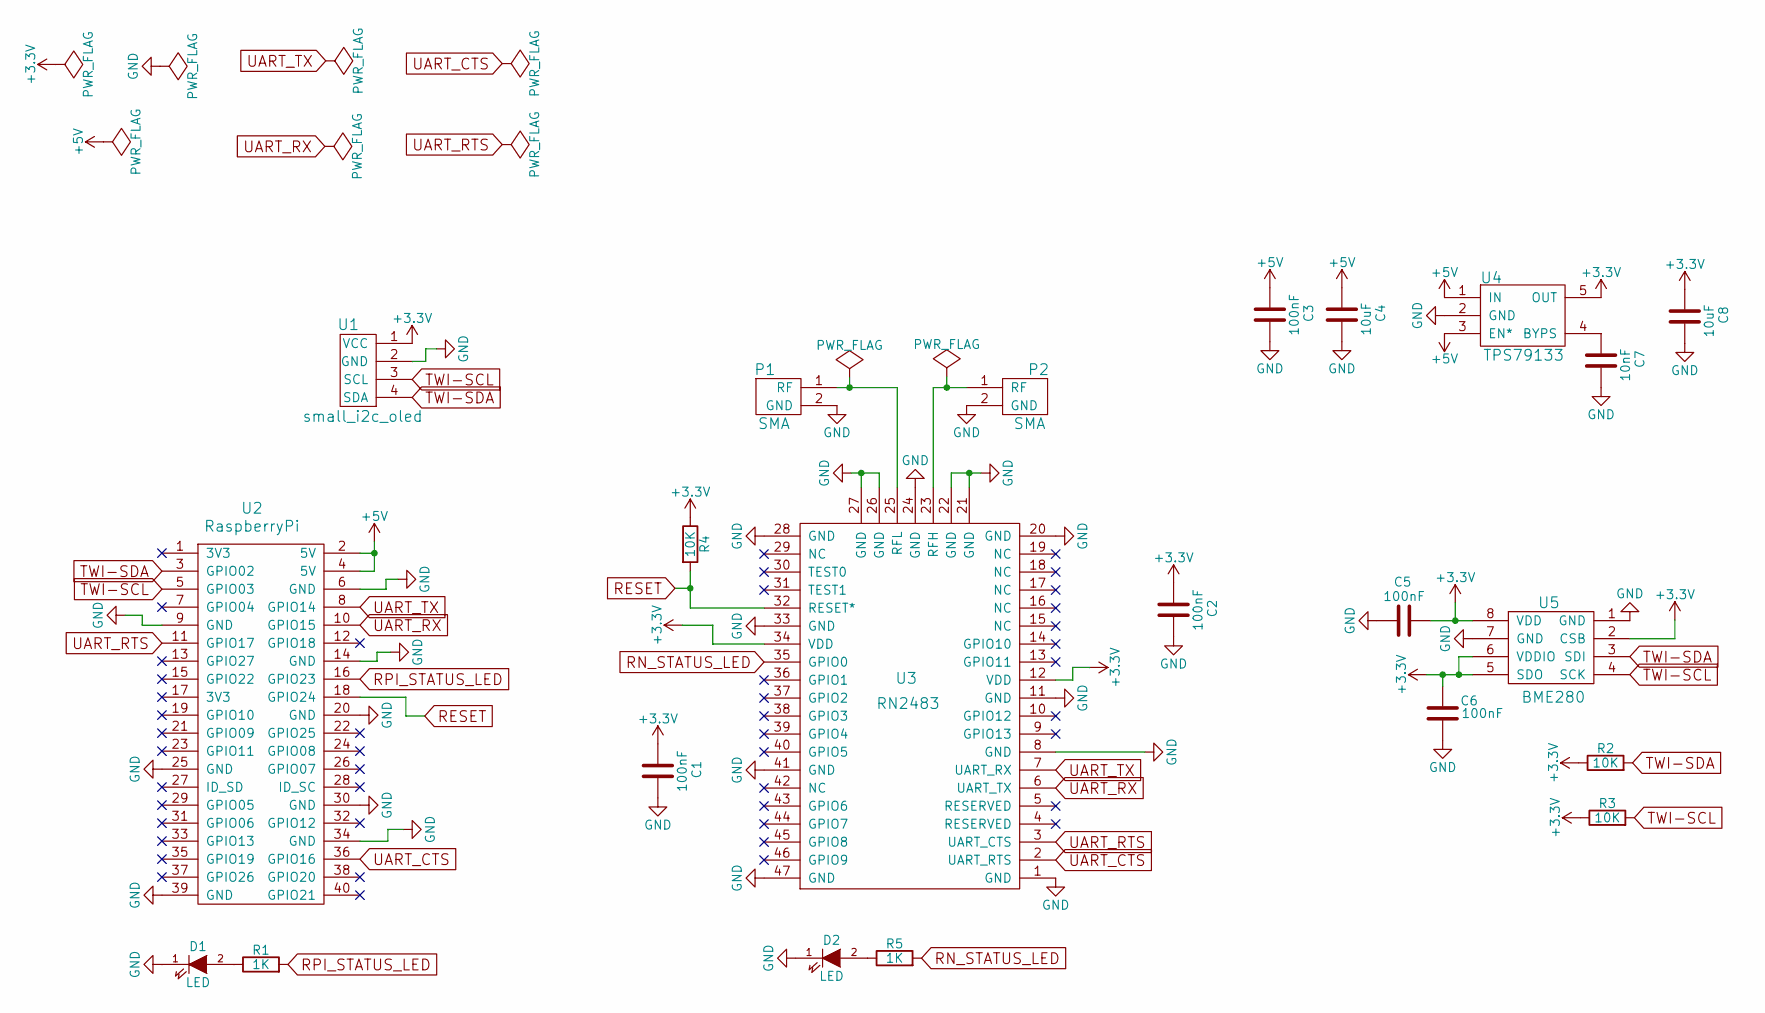
[picture p166: schematic gateway-module.sch]

Parts:
C1, C2, C3, C5, C6: 100nF; 0603_HandSoldering
C4, C8: 10uF; 0805_HandSoldering
C7: 10nF; 0603_HandSoldering
D1, D2: LED; LED_0603_HandSoldering
P1, P2: SMA; SMA_coax
R1, R5: 1K; 0603_HandSoldering
R2, R3, R4: 10K; 0603_HandSoldering
U1: small_i2c_oled; Small_I2C_OLED
U2: RaspberryPi
U3: RN2483
U4: TPS79133
U5: BME280

Connections:
+3.3V: C1.1, C2.1, C5.2, C6.2, C8.1, R2.1, R3.1, R4.1, U1.1 (VCC), U3.12 (VDD), U3.34 (VDD), U4.5 (OUT), U5.2 (CSB), U5.5 (SDO), U5.6 (VDDIO), U5.8 (VDD)
+5V: C3.1, C4.1, U2.2 (5V), U2.4 (5V), U4.1 (IN), U4.3 (EN*)
GND: C1.2, C2.2, C3.2, C4.2, C5.1, C6.1, C7.2, C8.2, D1.1 (K), D2.1 (K), P1.2 (GND), P2.2 (GND), U1.2 (GND), U2.6 (GND), U2.9 (GND), U2.14 (GND), U2.20 (GND), U2.25 (GND), U2.30 (GND), U2.34 (GND), U2.39 (GND), U3.1 (GND), U3.8 (GND), U3.11 (GND), U3.20 (GND), U3.21 (GND), U3.22 (GND), U3.24 (GND), U3.26 (GND), U3.27 (GND), U3.28 (GND), U3.33 (GND), U3.41 (GND), U3.47 (GND), U4.2 (GND), U5.1 (GND), U5.7 (GND)
unnamed: C7.1, U4.4 (BYPS)
unnamed: D1.2 (A), R1.1
unnamed: D2.2 (A), R5.1
unnamed: P1.1 (RF), U3.25 (RFL)
unnamed: P2.1 (RF), U3.23 (RFH)
RESET: R4.2, U2.18 (GPIO24), U3.32 (RESET*)
RN_STATUS_LED: R5.2, U3.35 (GPIO0)
RPI_STATUS_LED: R1.2, U2.16 (GPIO23)
TWI-SCL: R3.2, U1.3 (SCL), U2.5 (GPIO03), U5.4 (SCK)
TWI-SDA: R2.2, U1.4 (SDA), U2.3 (GPIO02), U5.3 (SDI)
UART_CTS: U2.36 (GPIO16), U3.2 (UART_RTS)
UART_RTS: U2.11 (GPIO17), U3.3 (UART_CTS)
UART_RX: U2.10 (GPIO15), U3.6 (UART_TX)
UART_TX: U2.8 (GPIO14), U3.7 (UART_RX)
